artsi0m/6sem_coursework/img/first_attempt/Part1-empty-sst-freq-1-Amplitude-Amplitude1.jpg

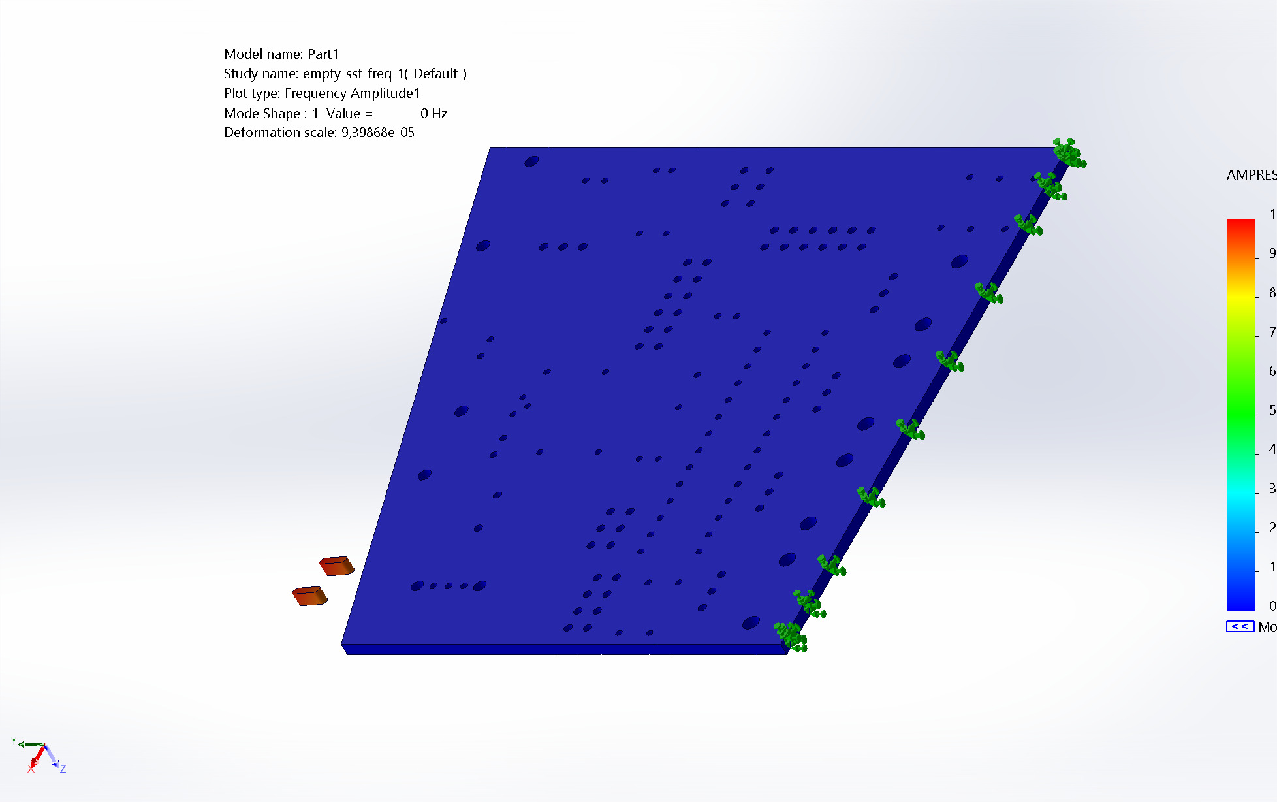
img/first_attempt/Part1-empty-sst-freq-1-Amplitude-Amplitude1.jpg
