artsi0m/6sem_coursework/img/first_attempt/simplified-Frequency 1-Quality-Quality1.jpg

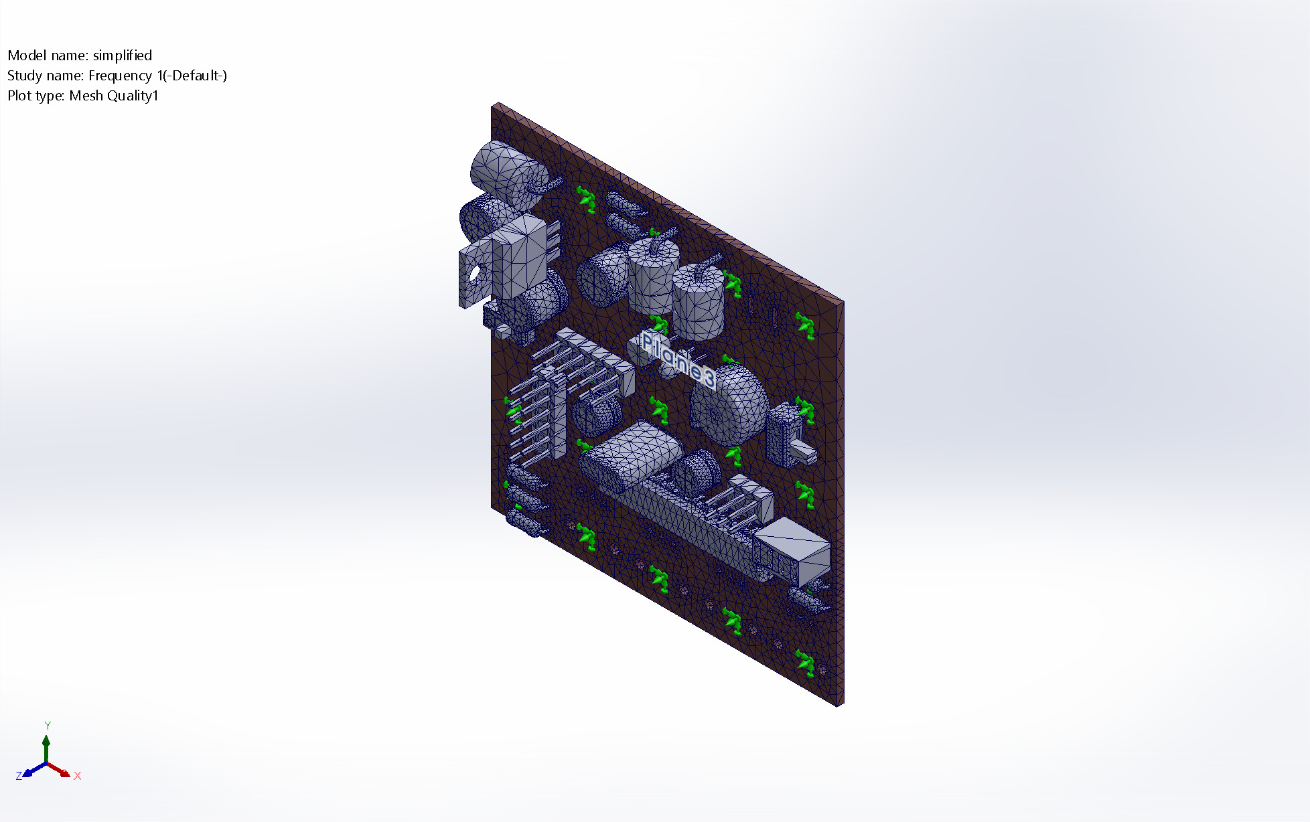
img/first_attempt/simplified-Frequency 1-Quality-Quality1.jpg
