artsi0m/6sem_coursework/img/first_attempt/sst-sst-1-freq-3-Amplitude-Amplitude1.jpg

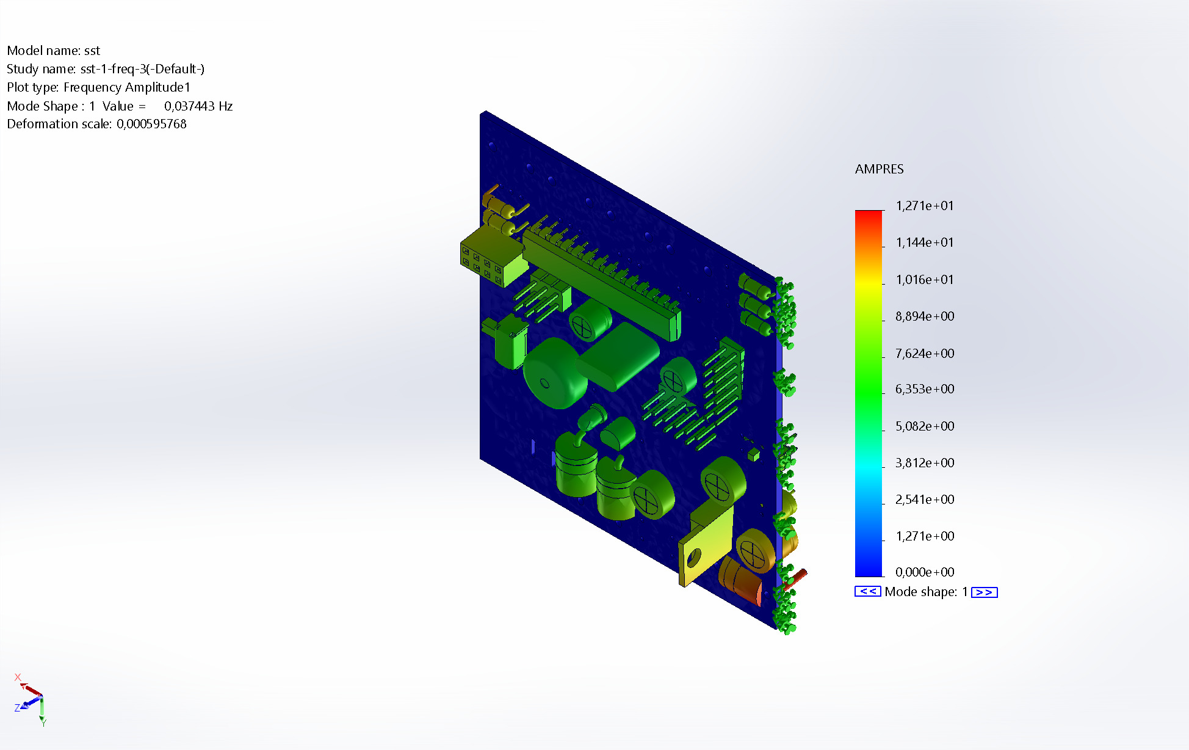
img/first_attempt/sst-sst-1-freq-3-Amplitude-Amplitude1.jpg
