artsi0m/6sem_coursework/img/first_attempt/sst_v3-sst-3-freq-2-Amplitude-Amplitude1.jpg

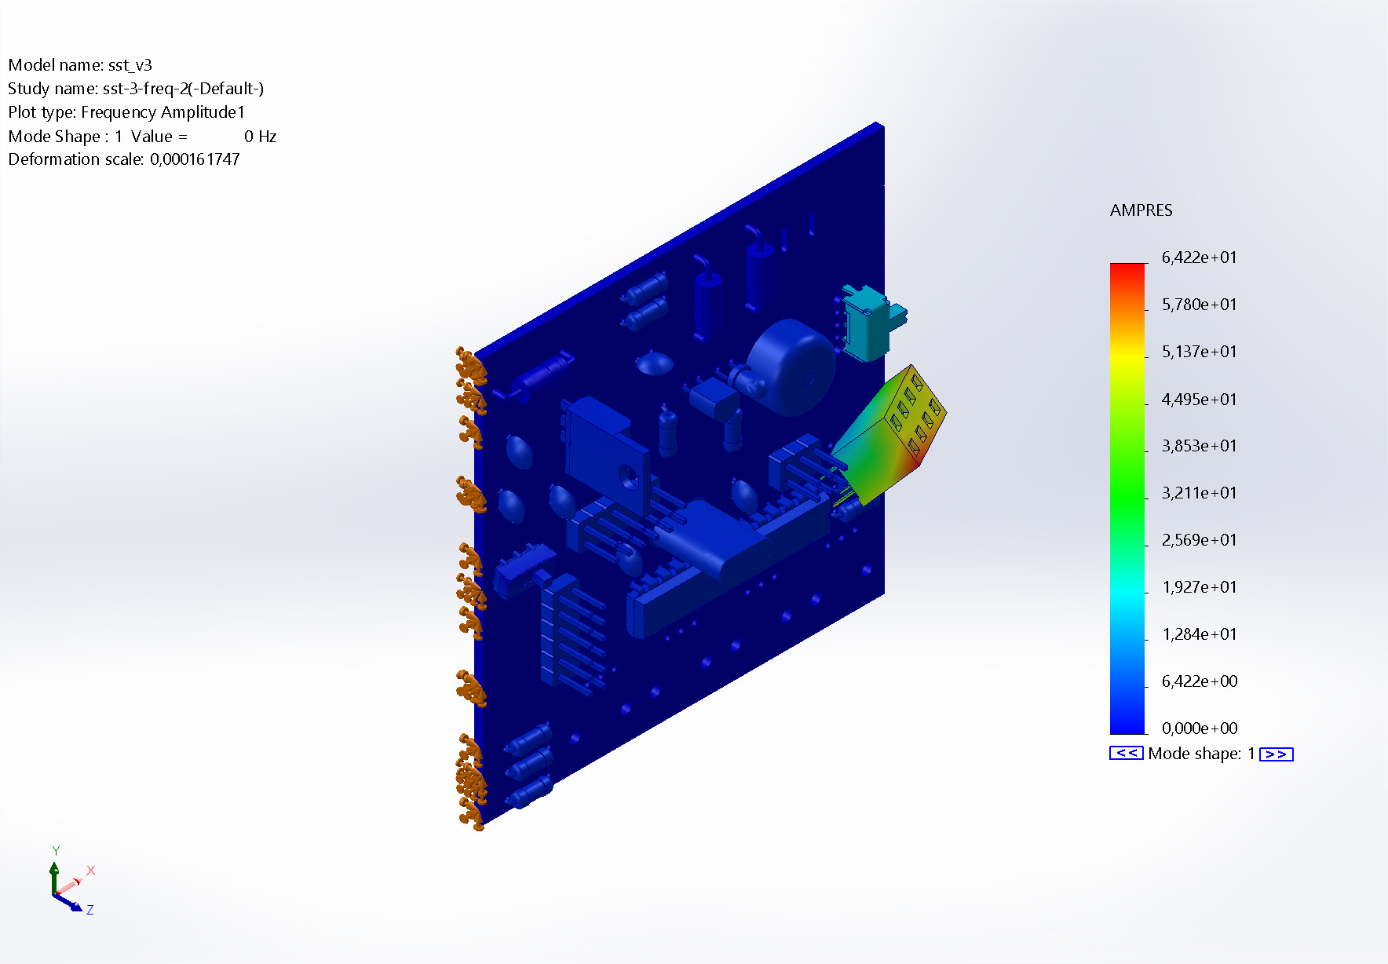
img/first_attempt/sst_v3-sst-3-freq-2-Amplitude-Amplitude1.jpg
