artsi0m/6sem_coursework/img/sst-1/comsol_static/sst-1-comsol-static.png

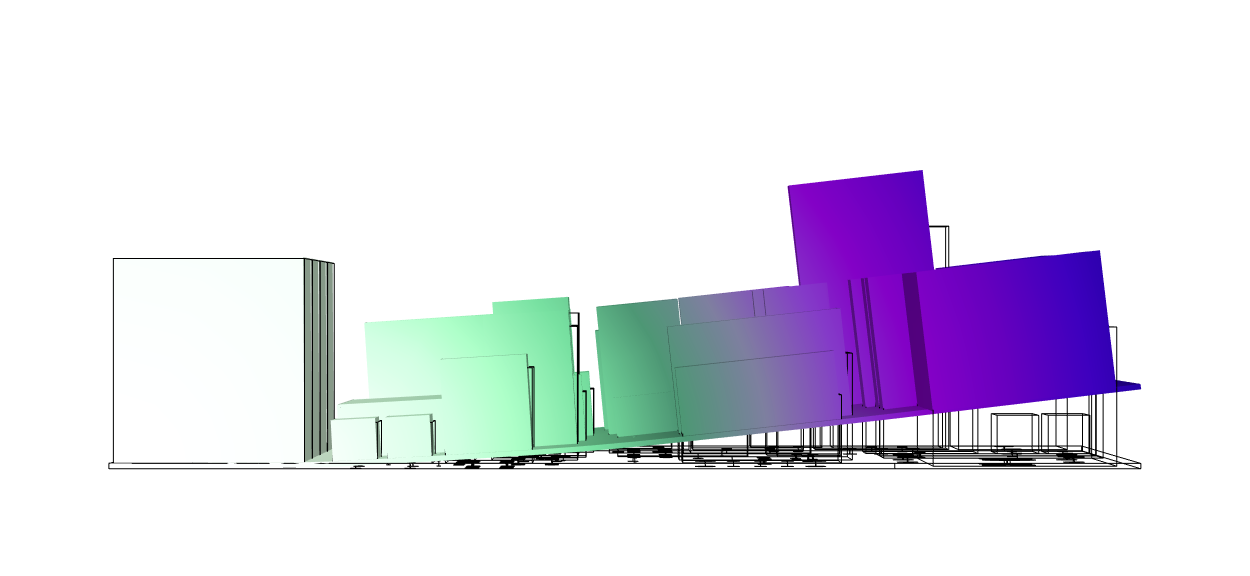
img/sst-1/comsol_static/sst-1-comsol-static.png
