artsi0m/6sem_coursework/img/sst-1/freq/sst-Freq-6-Amplitude-Amplitude1.jpg

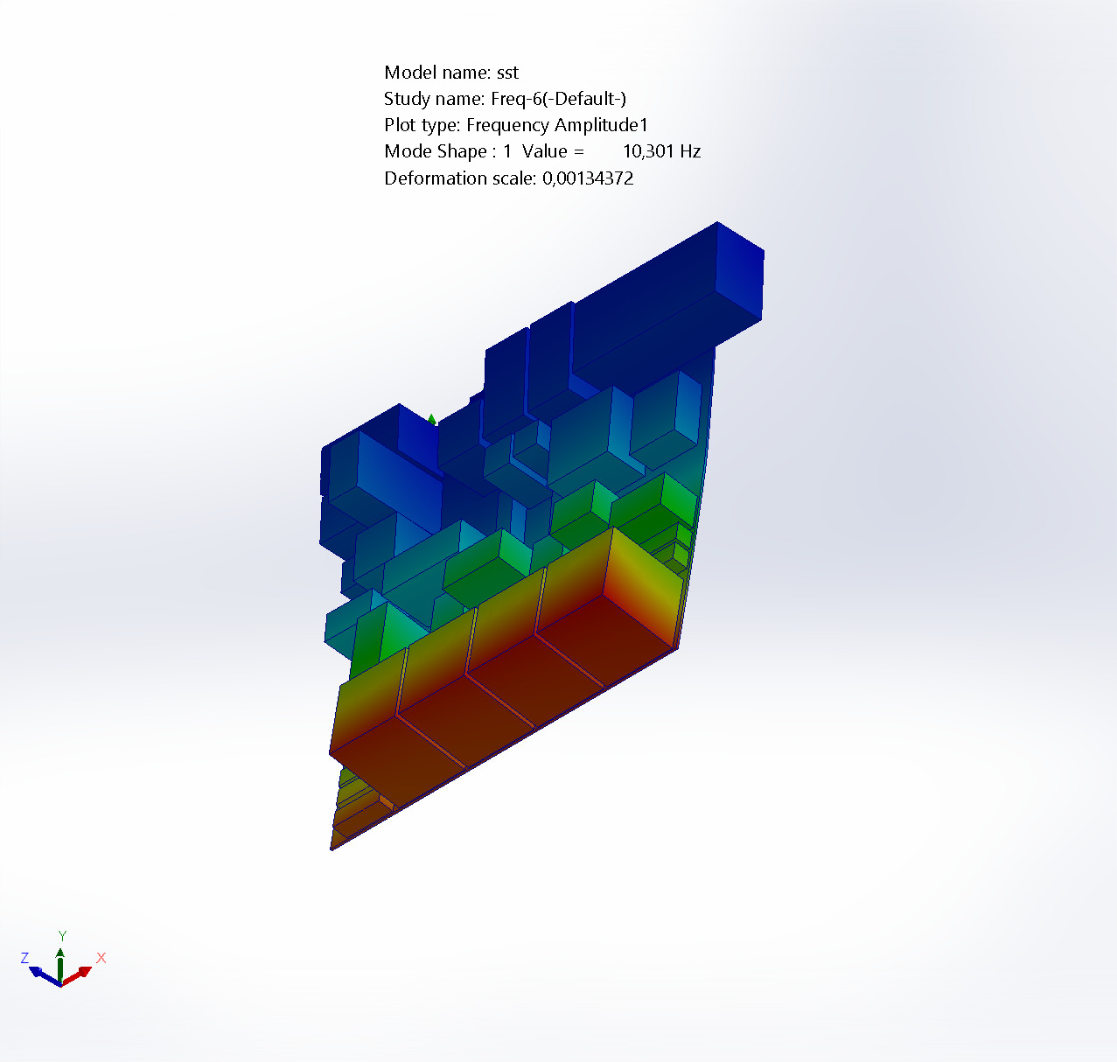
img/sst-1/freq/sst-Freq-6-Amplitude-Amplitude1.jpg
