artsi0m/6sem_coursework/img/sst-1/thermal/bottom_view.png

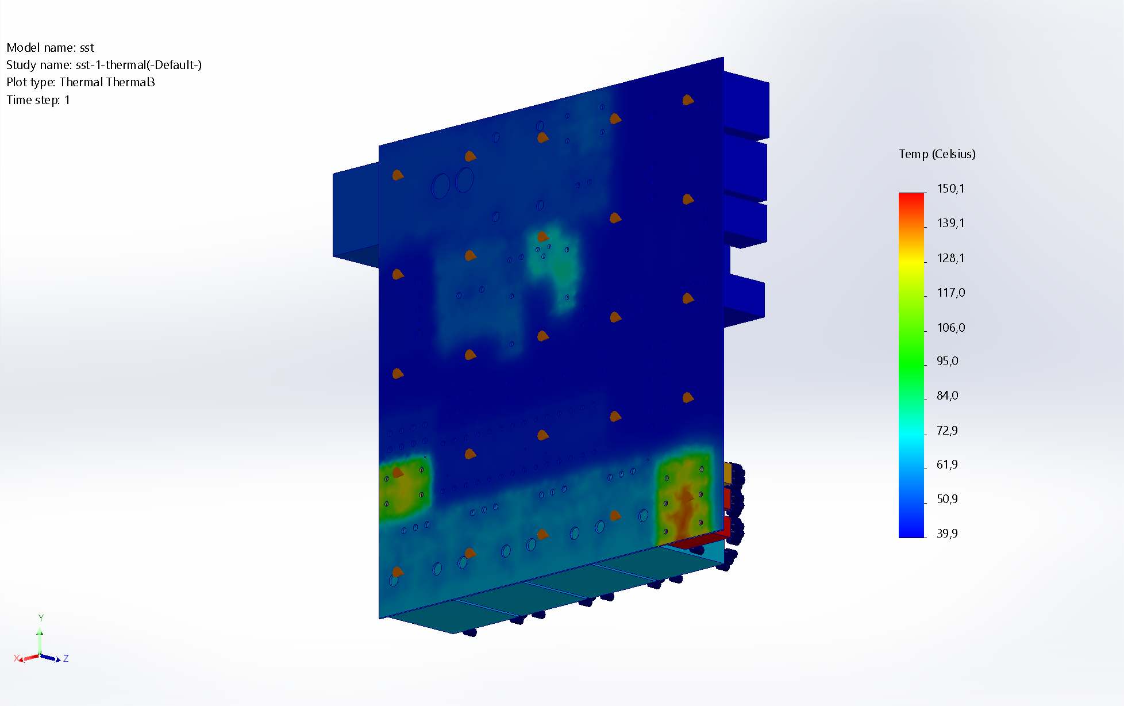
img/sst-1/thermal/bottom_view.png
