artsi0m/6sem_coursework/img/sst-2/freq/sst_v2-sst-2-freq-5-Amplitude-Amplitude1.jpg

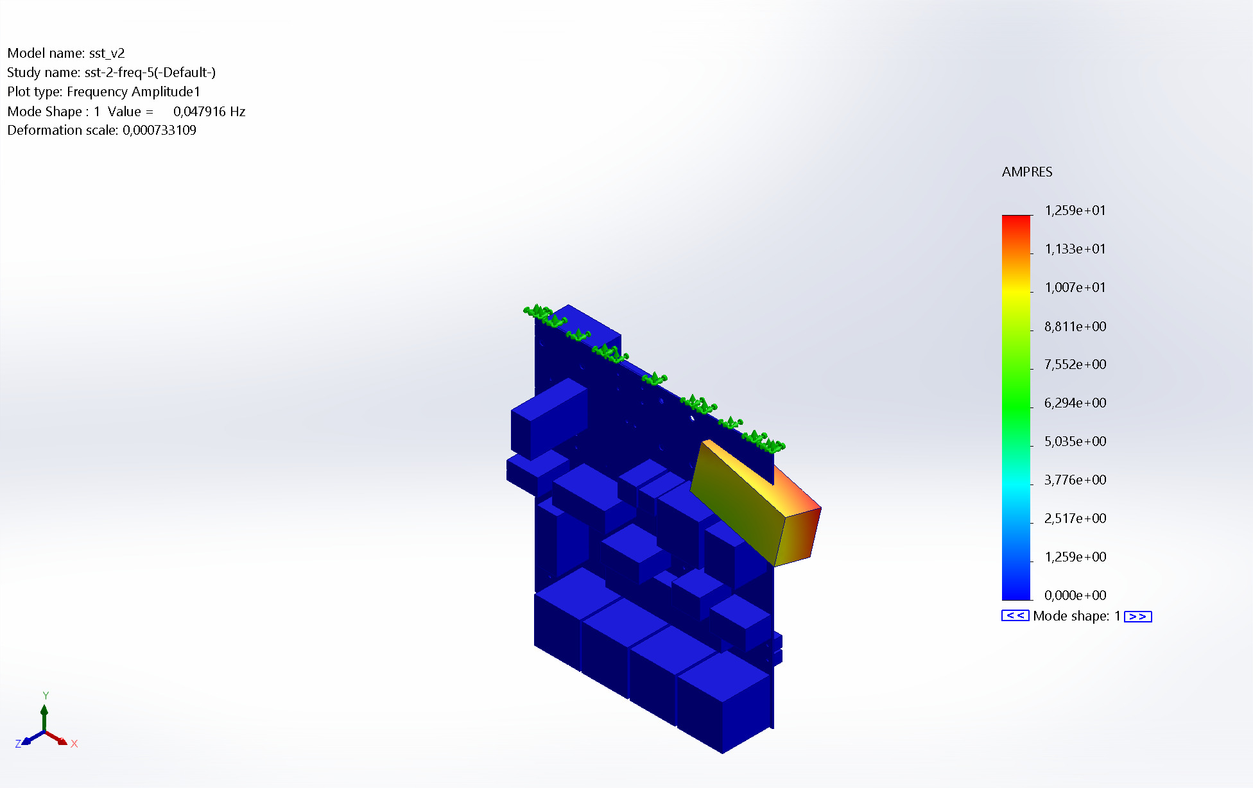
img/sst-2/freq/sst_v2-sst-2-freq-5-Amplitude-Amplitude1.jpg
