artsi0m/6sem_coursework/img/sst-2/thermal/bottom_view.png

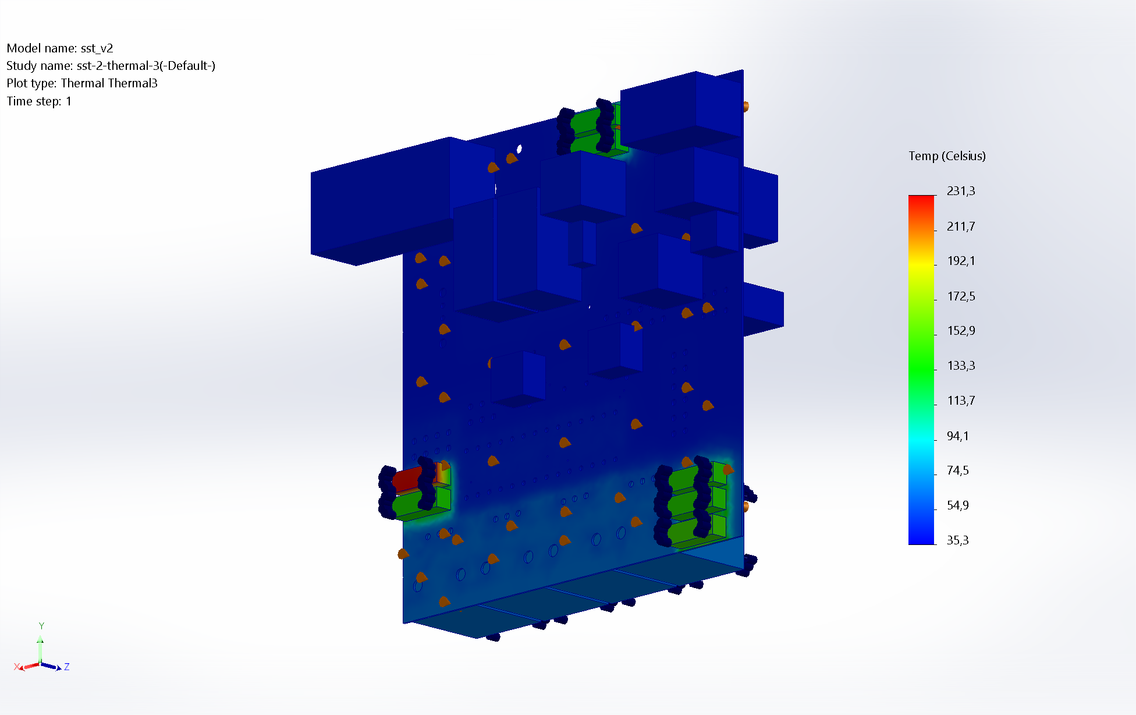
img/sst-2/thermal/bottom_view.png
