artsi0m/6sem_coursework/img/sst-2/thermal/sst_v2-sst-2-thermal-Thermal-Thermal1.jpg

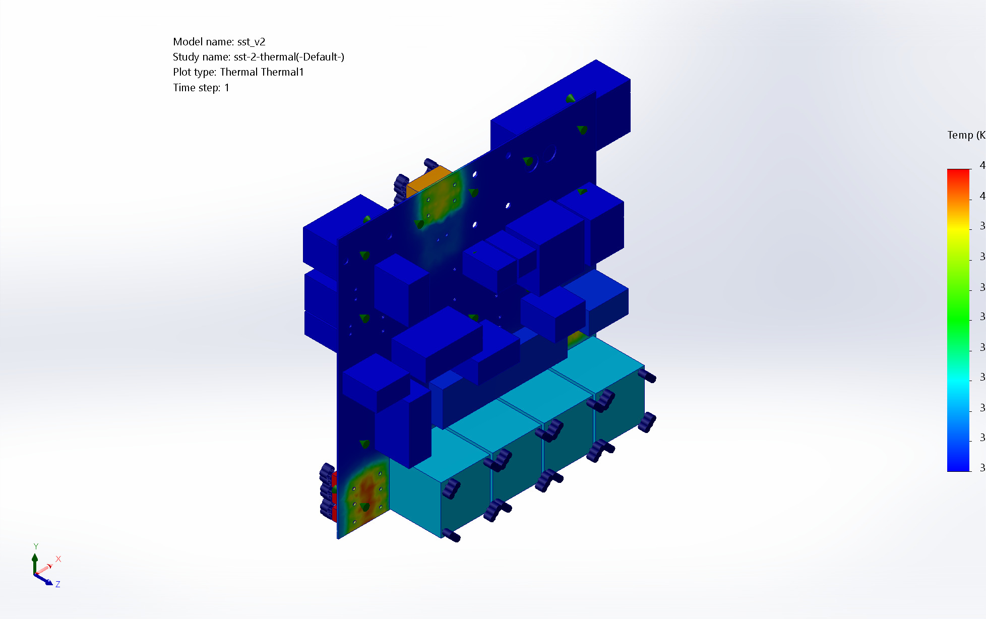
img/sst-2/thermal/sst_v2-sst-2-thermal-Thermal-Thermal1.jpg
