artsi0m/6sem_coursework/img/sst-3/freq/Frequency-v-CEMPF.png

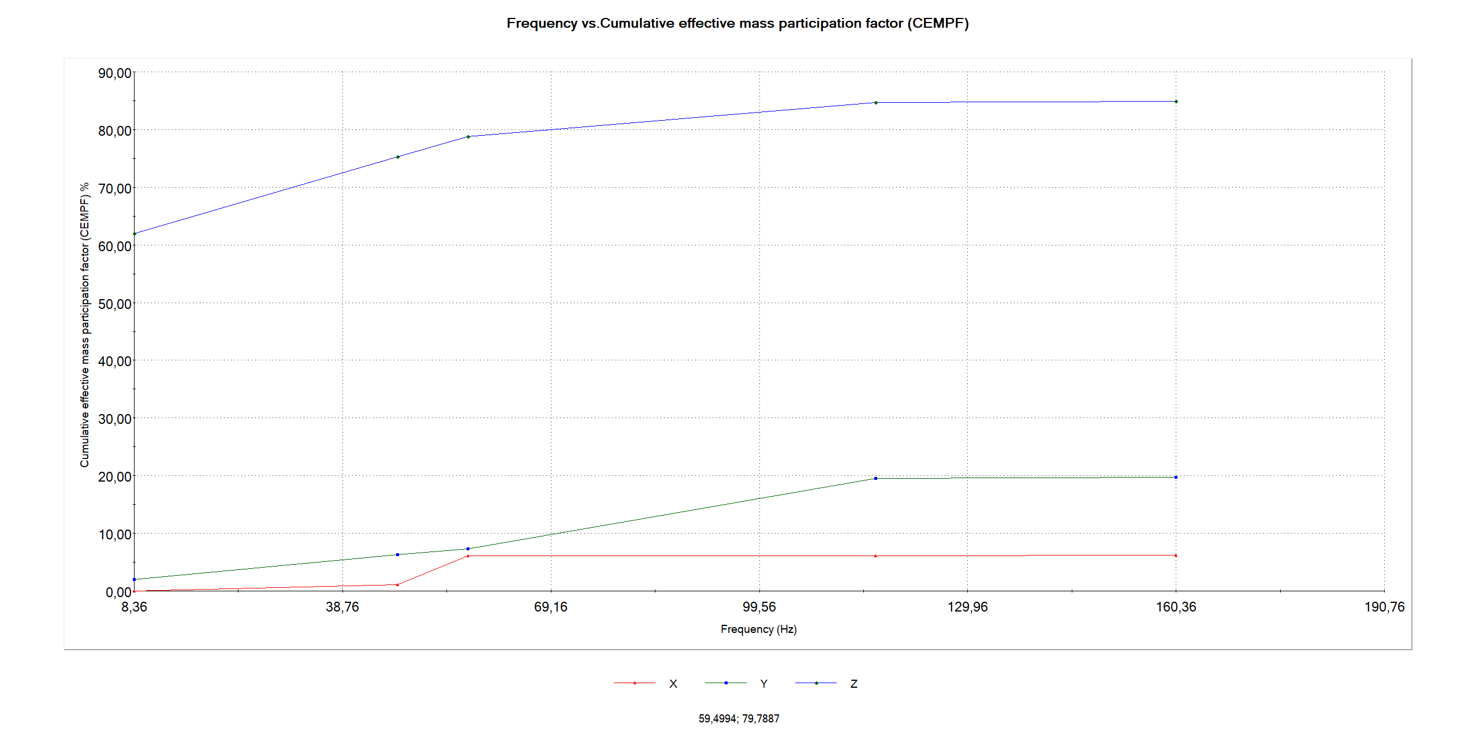
img/sst-3/freq/Frequency-v-CEMPF.png
