artsi0m/6sem_coursework/img/sst-3/freq/sst_v3-Freq-3-Amplitude-Amplitude3.jpg

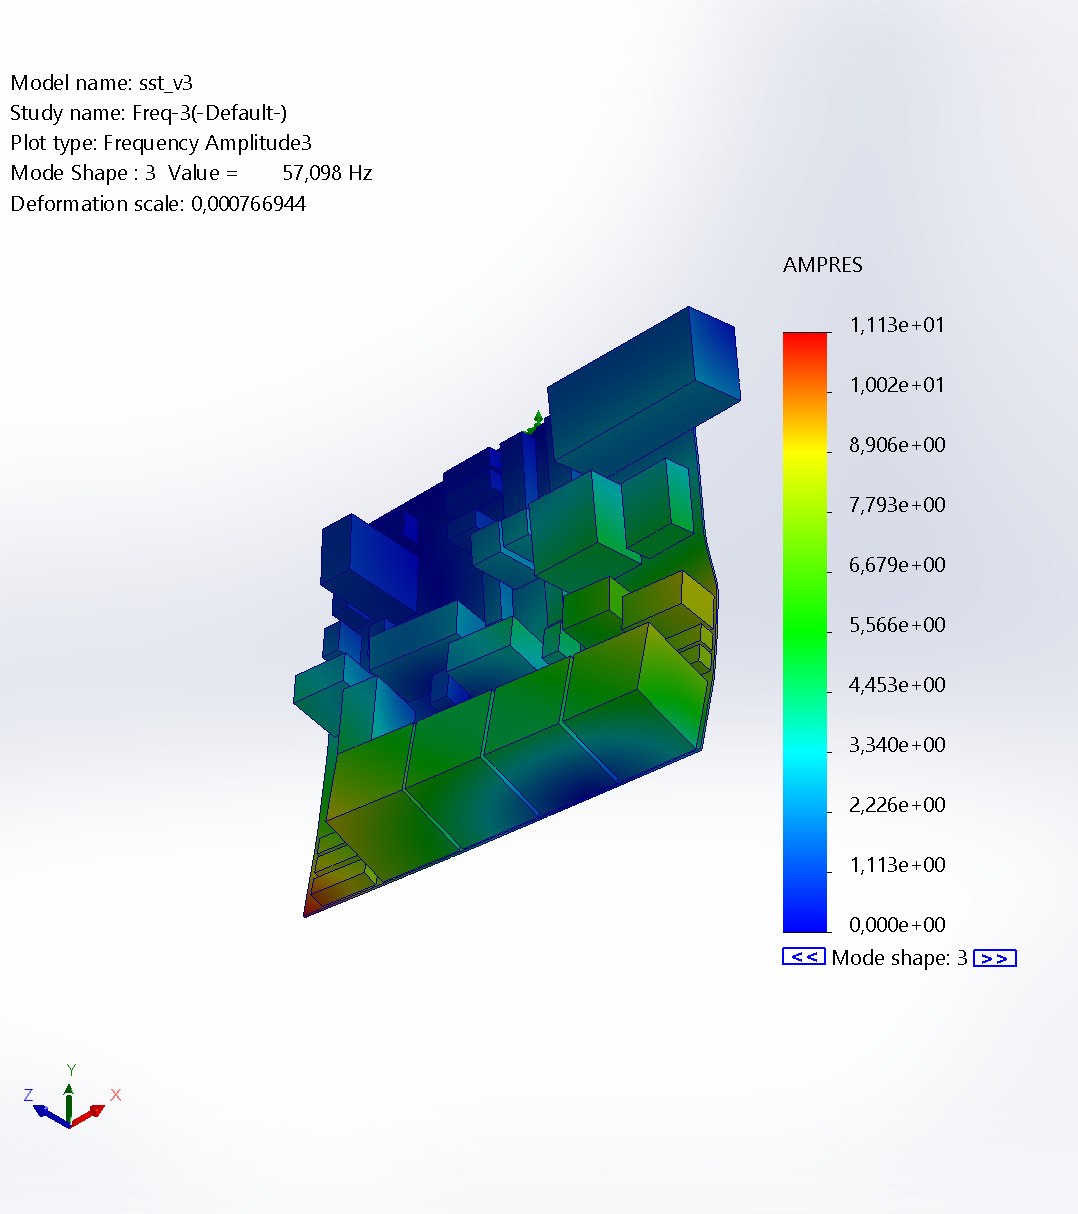
img/sst-3/freq/sst_v3-Freq-3-Amplitude-Amplitude3.jpg
