artsi0m/6sem_coursework/img/sst-3/freq/sst_v3-sst-3-freq-4-Amplitude-Amplitude3.jpg

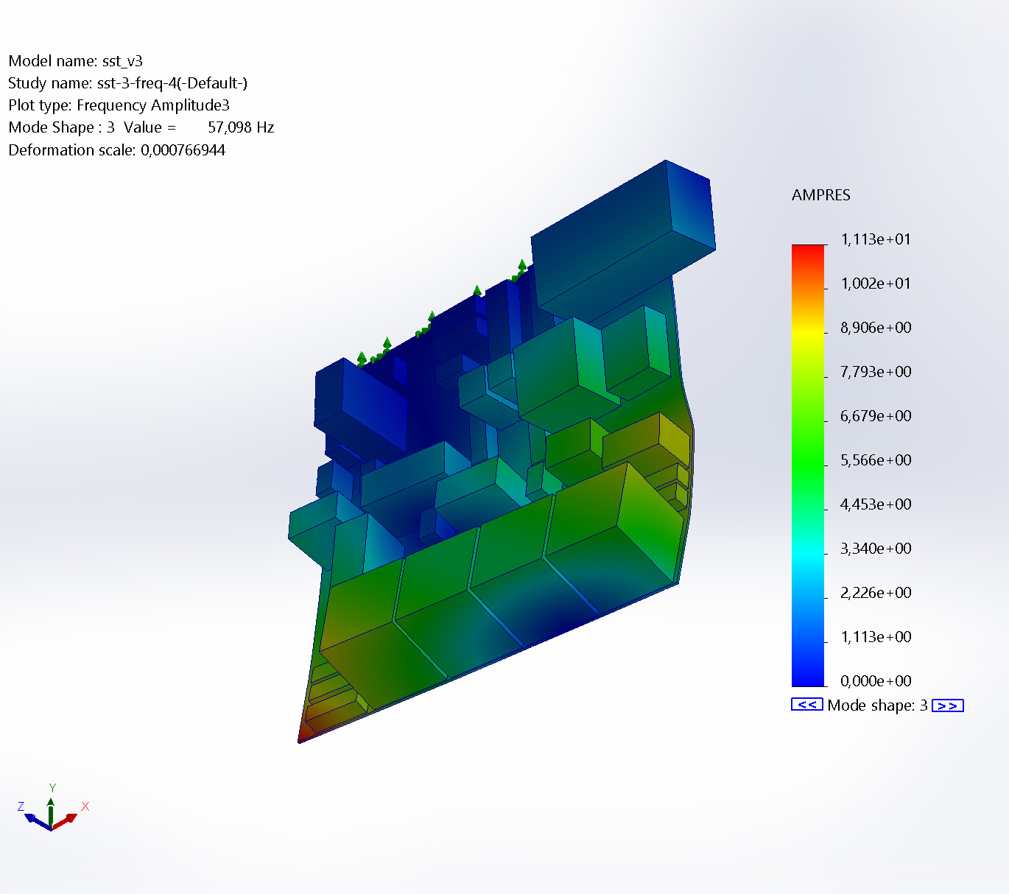
img/sst-3/freq/sst_v3-sst-3-freq-4-Amplitude-Amplitude3.jpg
