artsi0m/6sem_coursework/img/sst-3/freq/sst_v3-sst-3-freq-Frequency Response Graph-Frequency Response Graph1.jpg

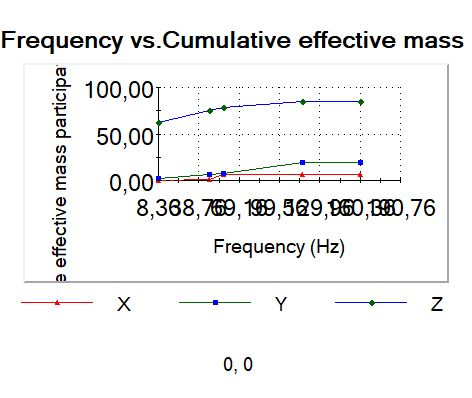
img/sst-3/freq/sst_v3-sst-3-freq-Frequency Response Graph-Frequency Response Graph1.jpg
