artsi0m/6sem_coursework/img/sst-3/thermal/bottom_view.png

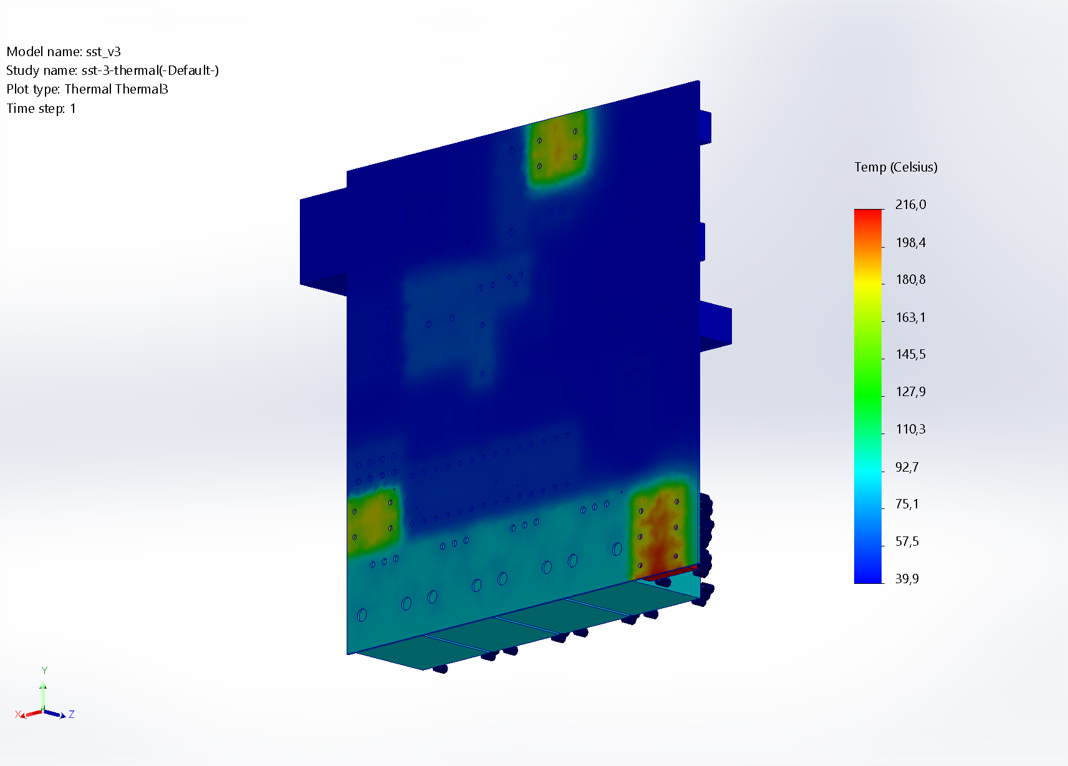
img/sst-3/thermal/bottom_view.png
